arithmaldor/PSX-Breakout/Photos/20190725_025241_1.gif

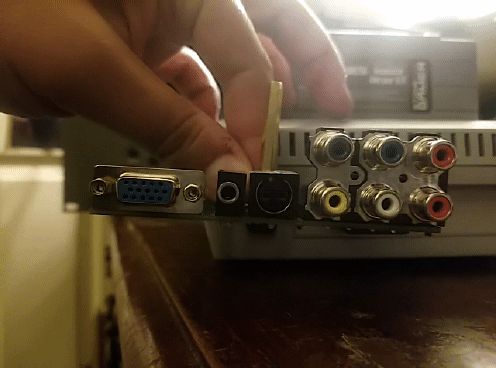
Photos/20190725_025241_1.gif
