arithmaldor/PSX-Breakout/Photos/20190729_005811.jpg

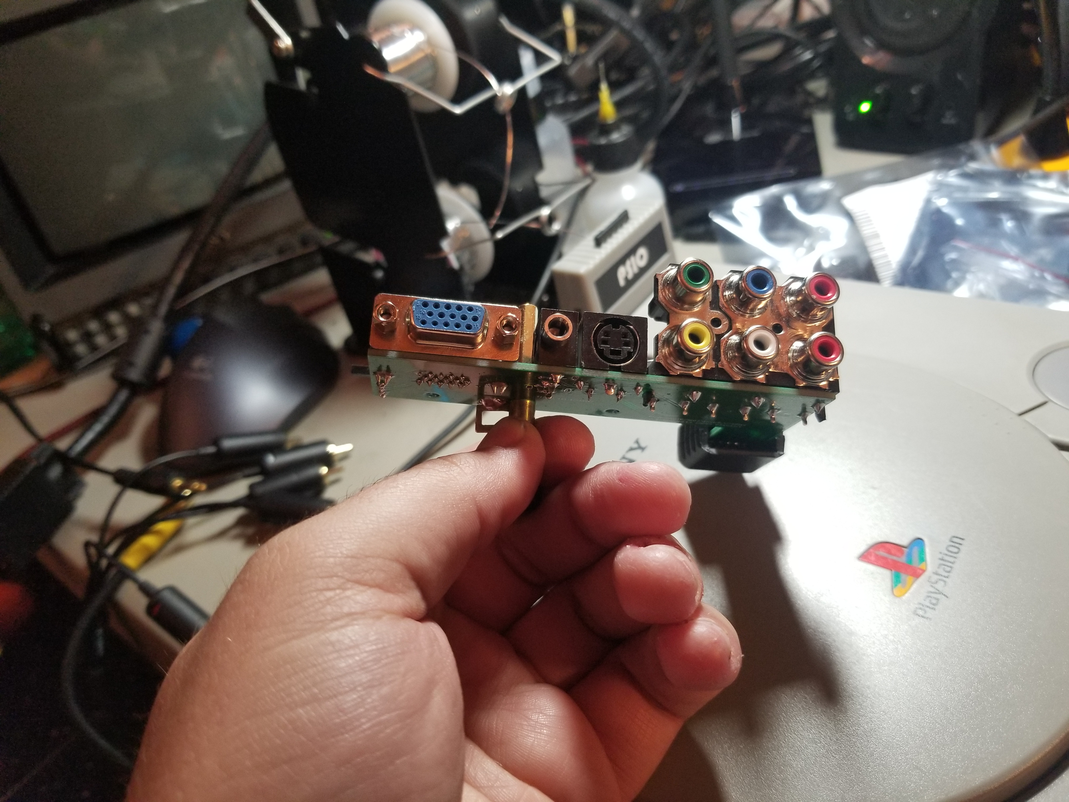
Photos/20190729_005811.jpg
