arithmaldor/PSX-Breakout/Photos/20190729_005817.jpg

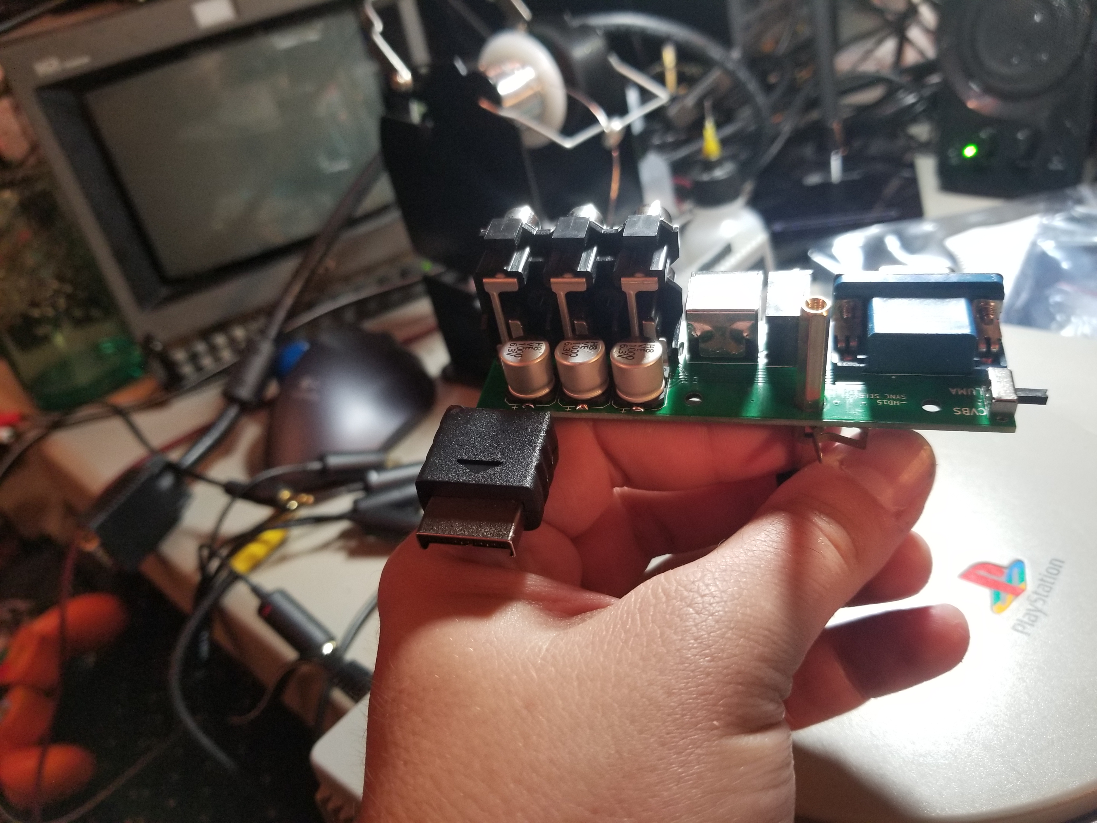
Photos/20190729_005817.jpg
